IDMIL/T-Tree/utils/led_off.py

"""CircuitPython Essentials NeoPixel example"""
import time
import board
from rainbowio import colorwheel
import neopixel

pixel_pin = board.D18
num_pixels = 4*8

pixels = neopixel.NeoPixel(pixel_pin, num_pixels, brightness=0.3, auto_write=False)

pixels.fill( (0,0,0) )
pixels.show()
